FedorKulaev/Spyglass_with_autofocus/Photo/IMG_20250610_153453.jpg

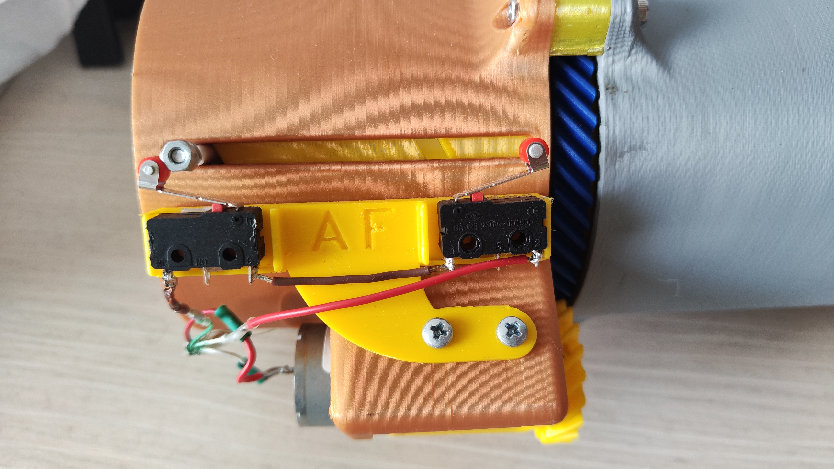
Photo/IMG_20250610_153453.jpg
