FedorKulaev/Spyglass_with_autofocus/Photo/photo_2025-06-21 00.15.36.jpeg

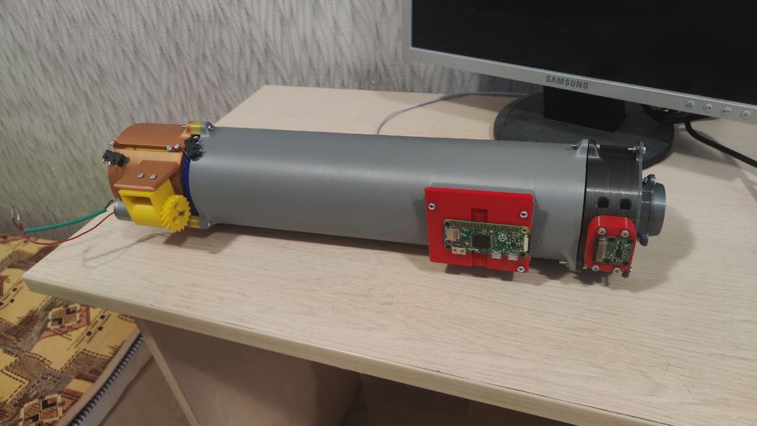
Photo/photo_2025-06-21 00.15.36.jpeg
